STE-Labs/legacy-84/Chassis/Galaxy/230/2U/docs/bottom-gx283.png

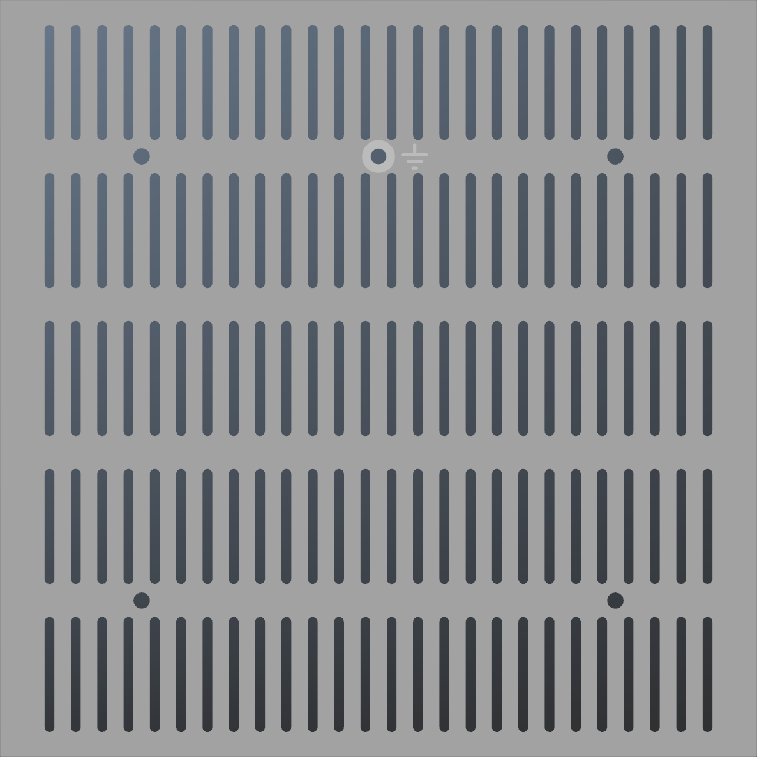
Chassis/Galaxy/230/2U/docs/bottom-gx283.png
