STE-Labs/legacy-84/Chassis/Galaxy/230/4U/docs/rear-xlr.png

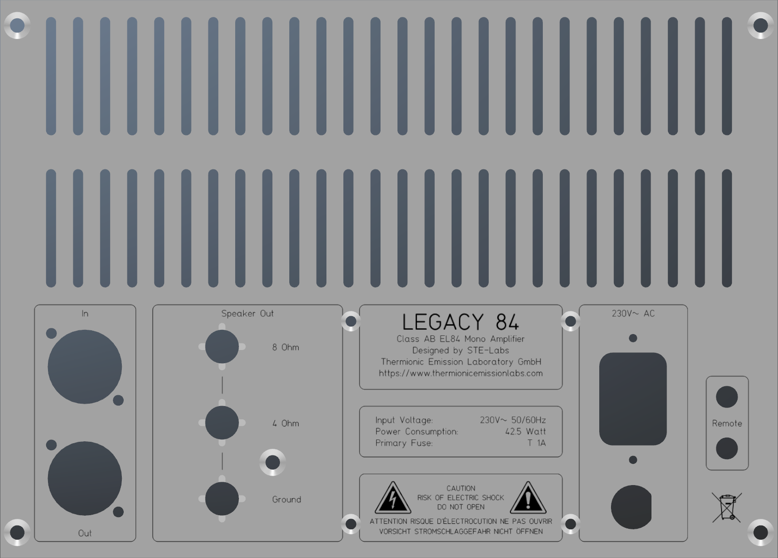
Chassis/Galaxy/230/4U/docs/rear-xlr.png
