STE-Labs/legacy-84/Chassis/Galaxy/330/2U/Renders/front-3-1.png

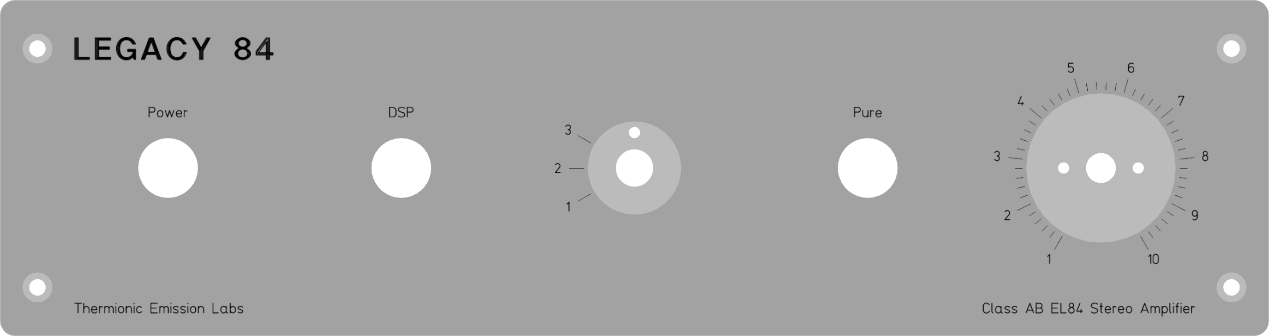
Chassis/Galaxy/330/2U/Renders/front-3-1.png
