STE-Labs/legacy-84/Chassis/Galaxy/330/2U/Renders/gx383-bottom.png

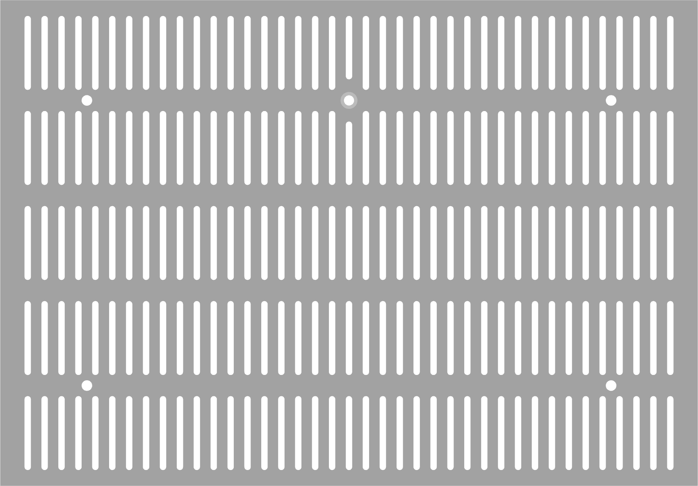
Chassis/Galaxy/330/2U/Renders/gx383-bottom.png
