STE-Labs/legacy-84/Chassis/Galaxy/330/2U/Renders/gx388-top.png

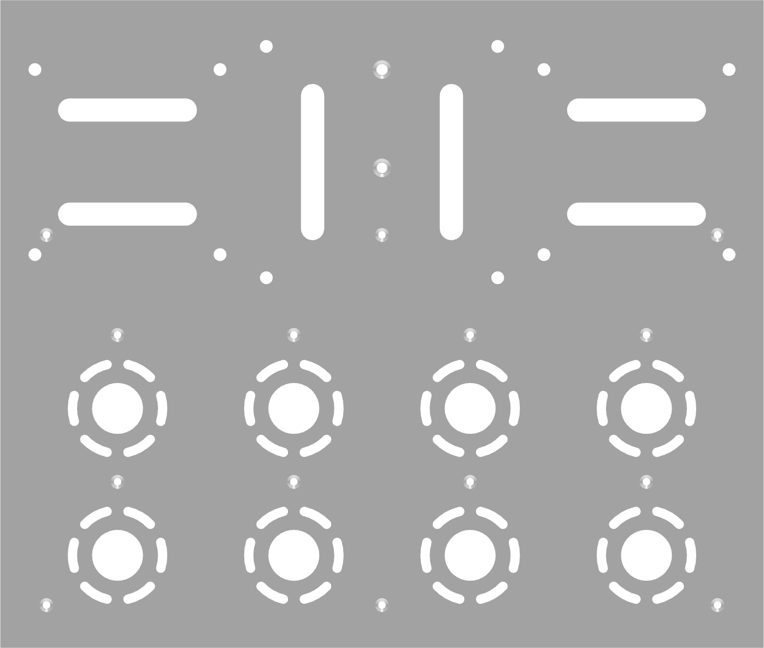
Chassis/Galaxy/330/2U/Renders/gx388-top.png
