STE-Labs/legacy-84/Chassis/Galaxy/330/2U/Renders/rear-3-1-xlr.png

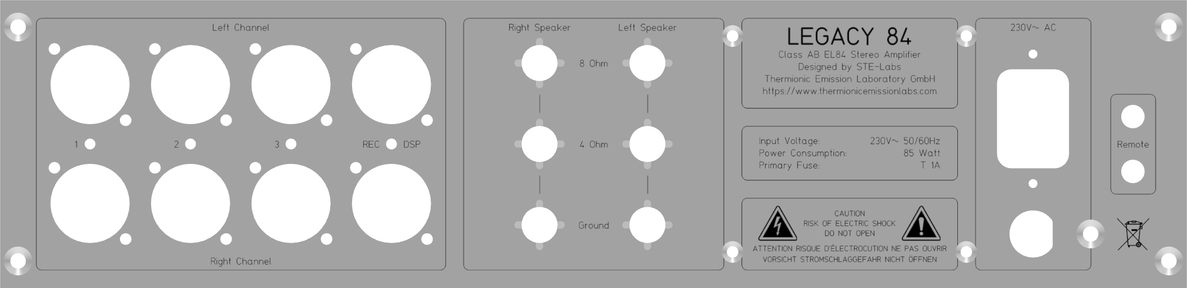
Chassis/Galaxy/330/2U/Renders/rear-3-1-xlr.png
