STE-Labs/legacy-84/Chassis/Galaxy/330/2U/Renders/rear-4-1-rca.png

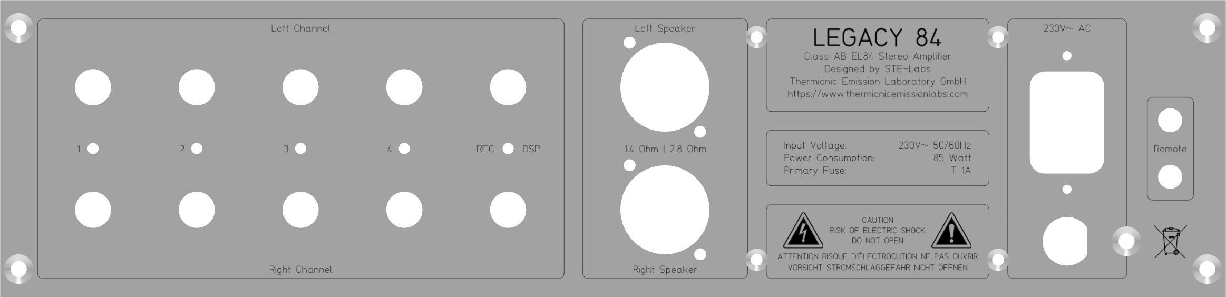
Chassis/Galaxy/330/2U/Renders/rear-4-1-rca.png
