STE-Labs/legacy-84/Chassis/Slimline/2U/docs/front.png

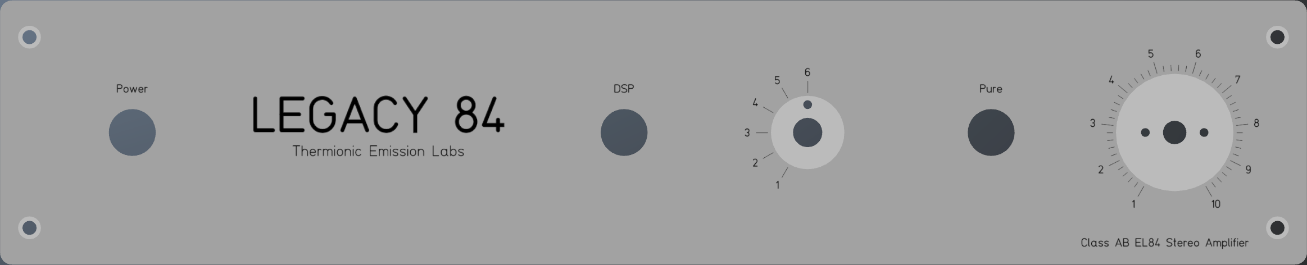
Chassis/Slimline/2U/docs/front.png
