STE-Labs/legacy-84/Chassis/Slimline/2U/docs/rear-xlr.png

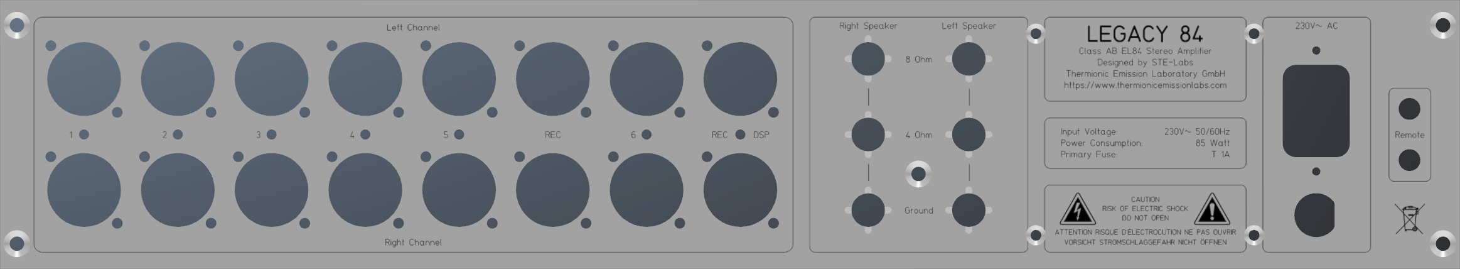
Chassis/Slimline/2U/docs/rear-xlr.png
