STE-Labs/legacy-84/transformers/AEE/open/1000014716.jpg

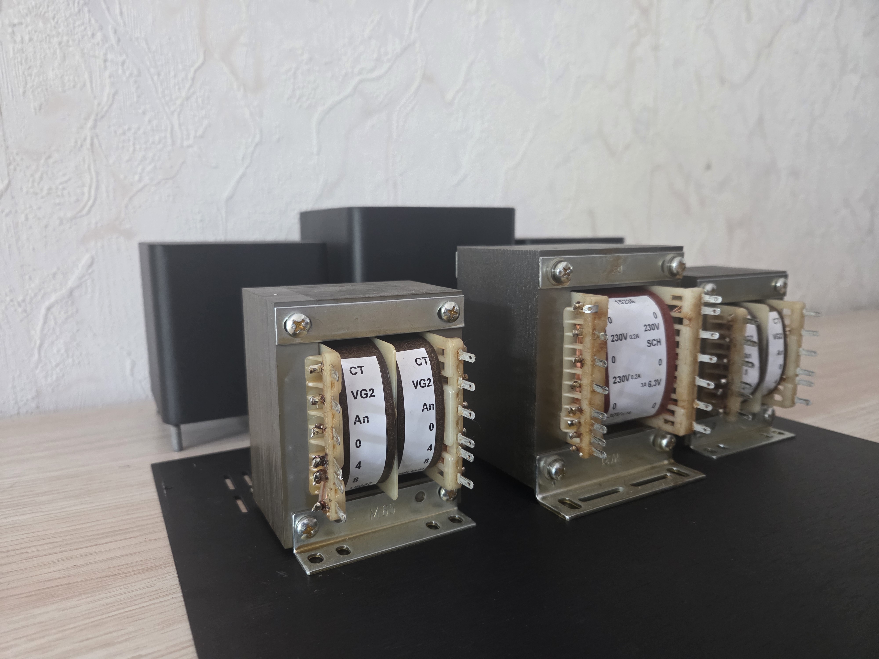
transformers/AEE/open/1000014716.jpg
