STE-Labs/legacy-84/transformers/AEE/open/1000014717.jpg

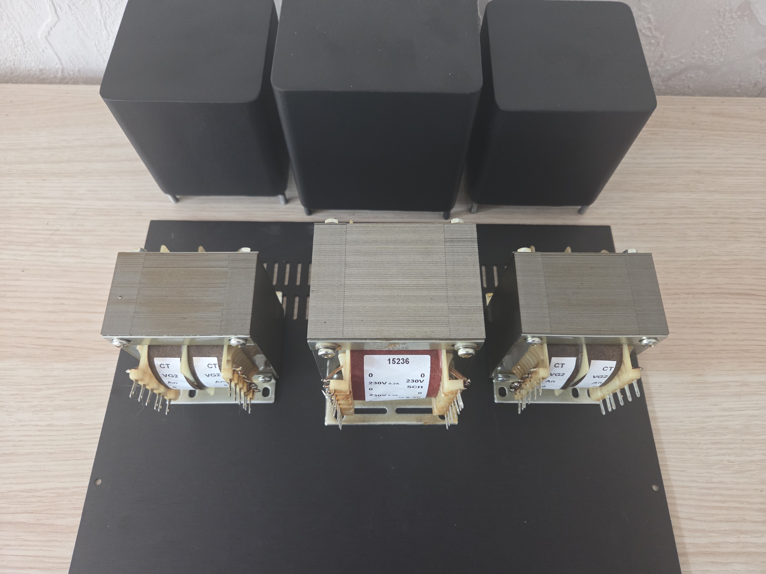
transformers/AEE/open/1000014717.jpg
