STE-Labs/legacy-84/transformers/AEE/open/1000014719.jpg

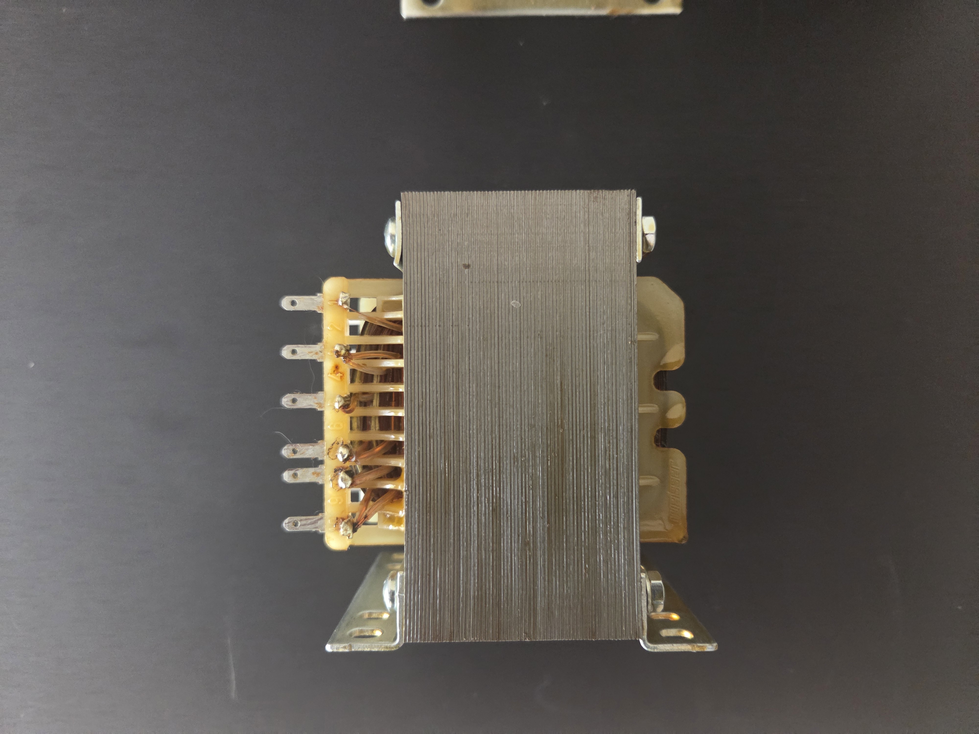
transformers/AEE/open/1000014719.jpg
