STE-Labs/legacy-84/transformers/AEE/open/1000014720.jpg

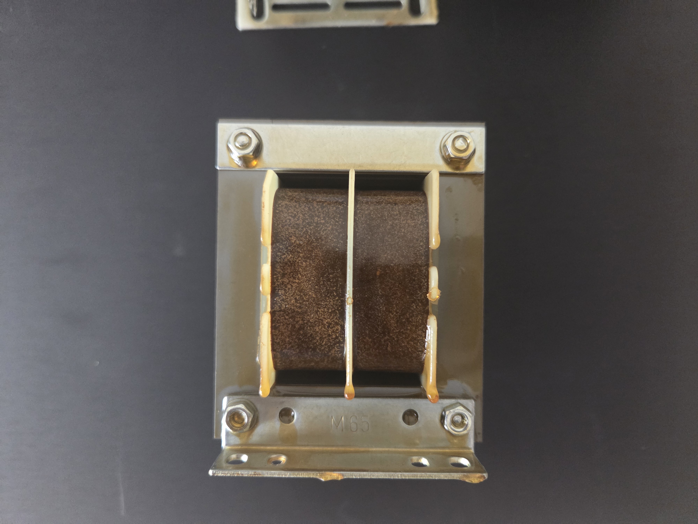
transformers/AEE/open/1000014720.jpg
