STE-Labs/legacy-84/transformers/AEE/open/1000014721.jpg

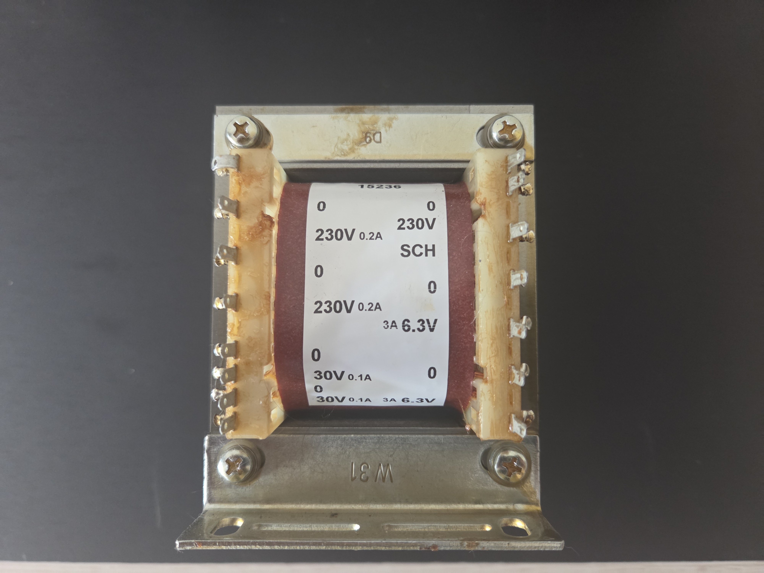
transformers/AEE/open/1000014721.jpg
