STE-Labs/legacy-84/transformers/AEE/potted/1000014724.jpg

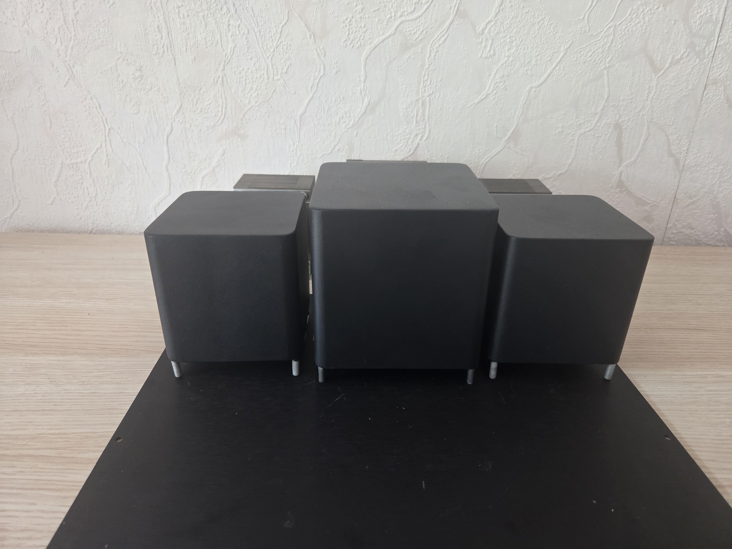
transformers/AEE/potted/1000014724.jpg
