STE-Labs/legacy-84/transformers/AEE/potted/1000014725.jpg

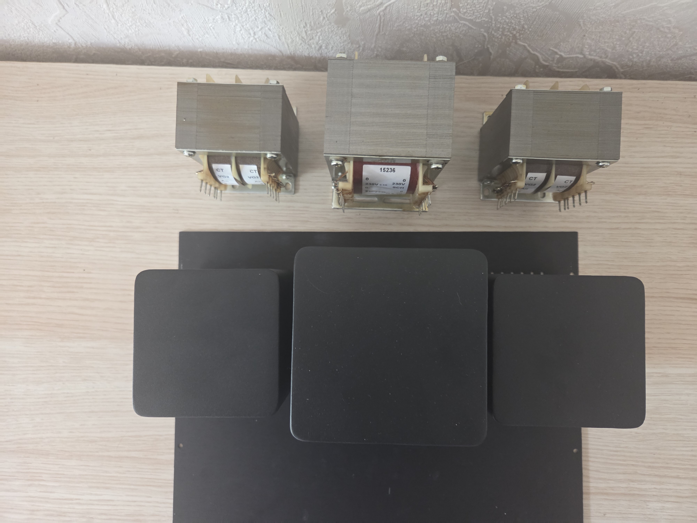
transformers/AEE/potted/1000014725.jpg
