STE-Labs/legacy-84/transformers/AEE/potted/1000014728.jpg

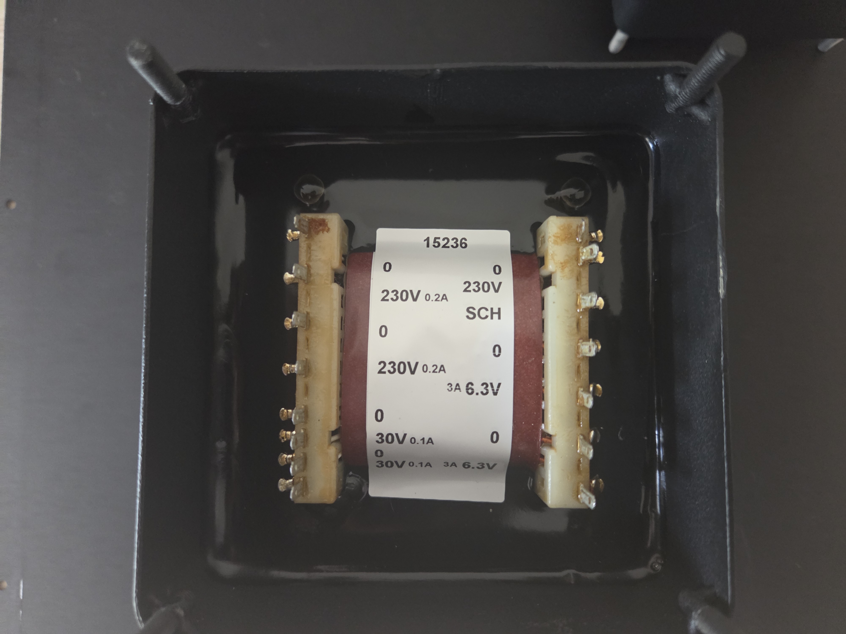
transformers/AEE/potted/1000014728.jpg
