STE-Labs/legacy-84/transformers/AEE/potted/1000014729.jpg

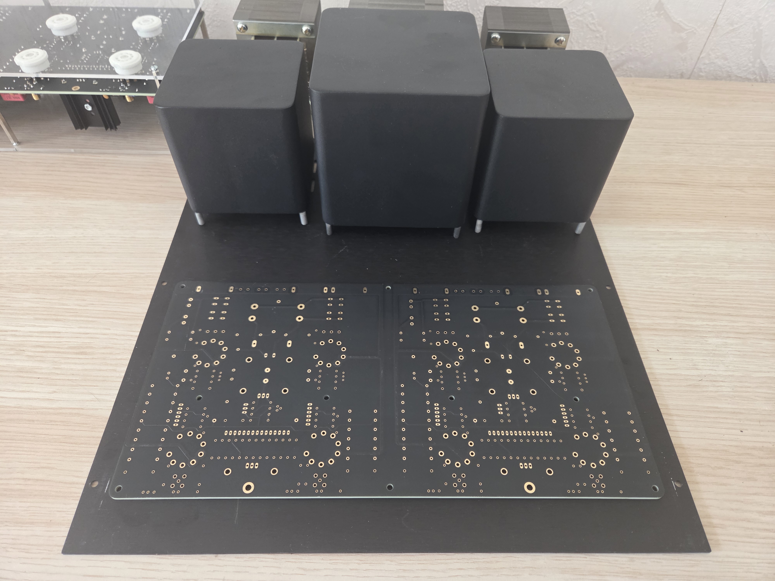
transformers/AEE/potted/1000014729.jpg
