STE-Labs/legacy-84/legacy-84-mono-inverted/docs/circuit-diagram-pure-switch.pdf

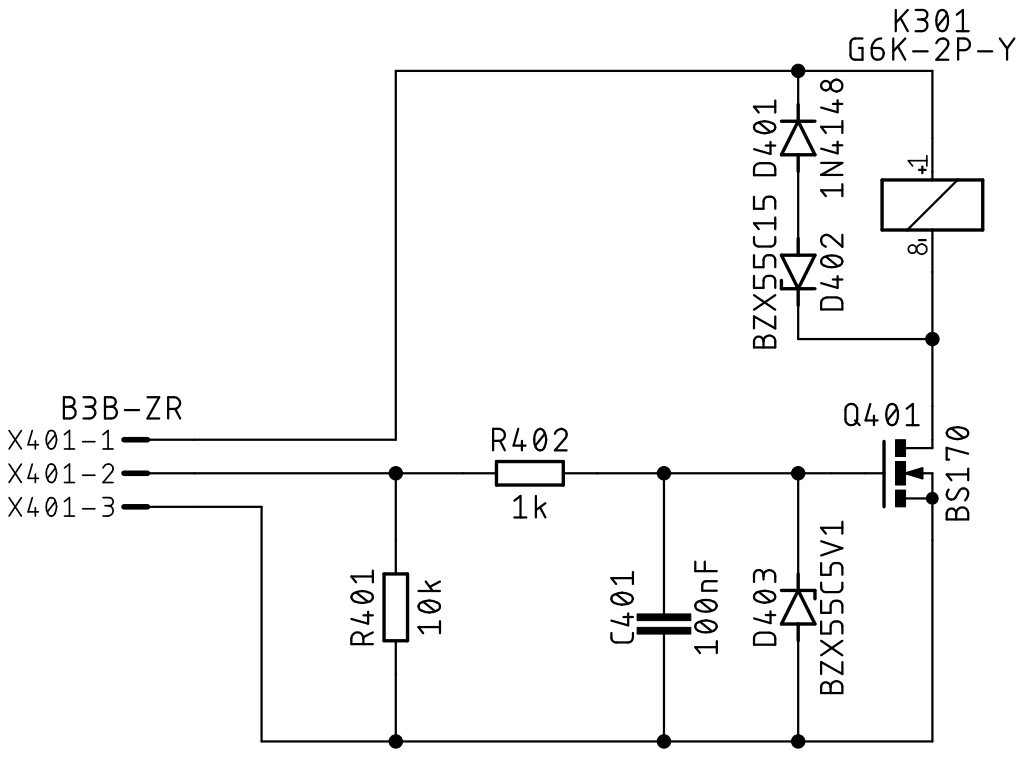
[picture p122: page 1]
