STE-Labs/legacy-84/legacy-84-mono/docs/circuit-diagram-amplifier.pdf

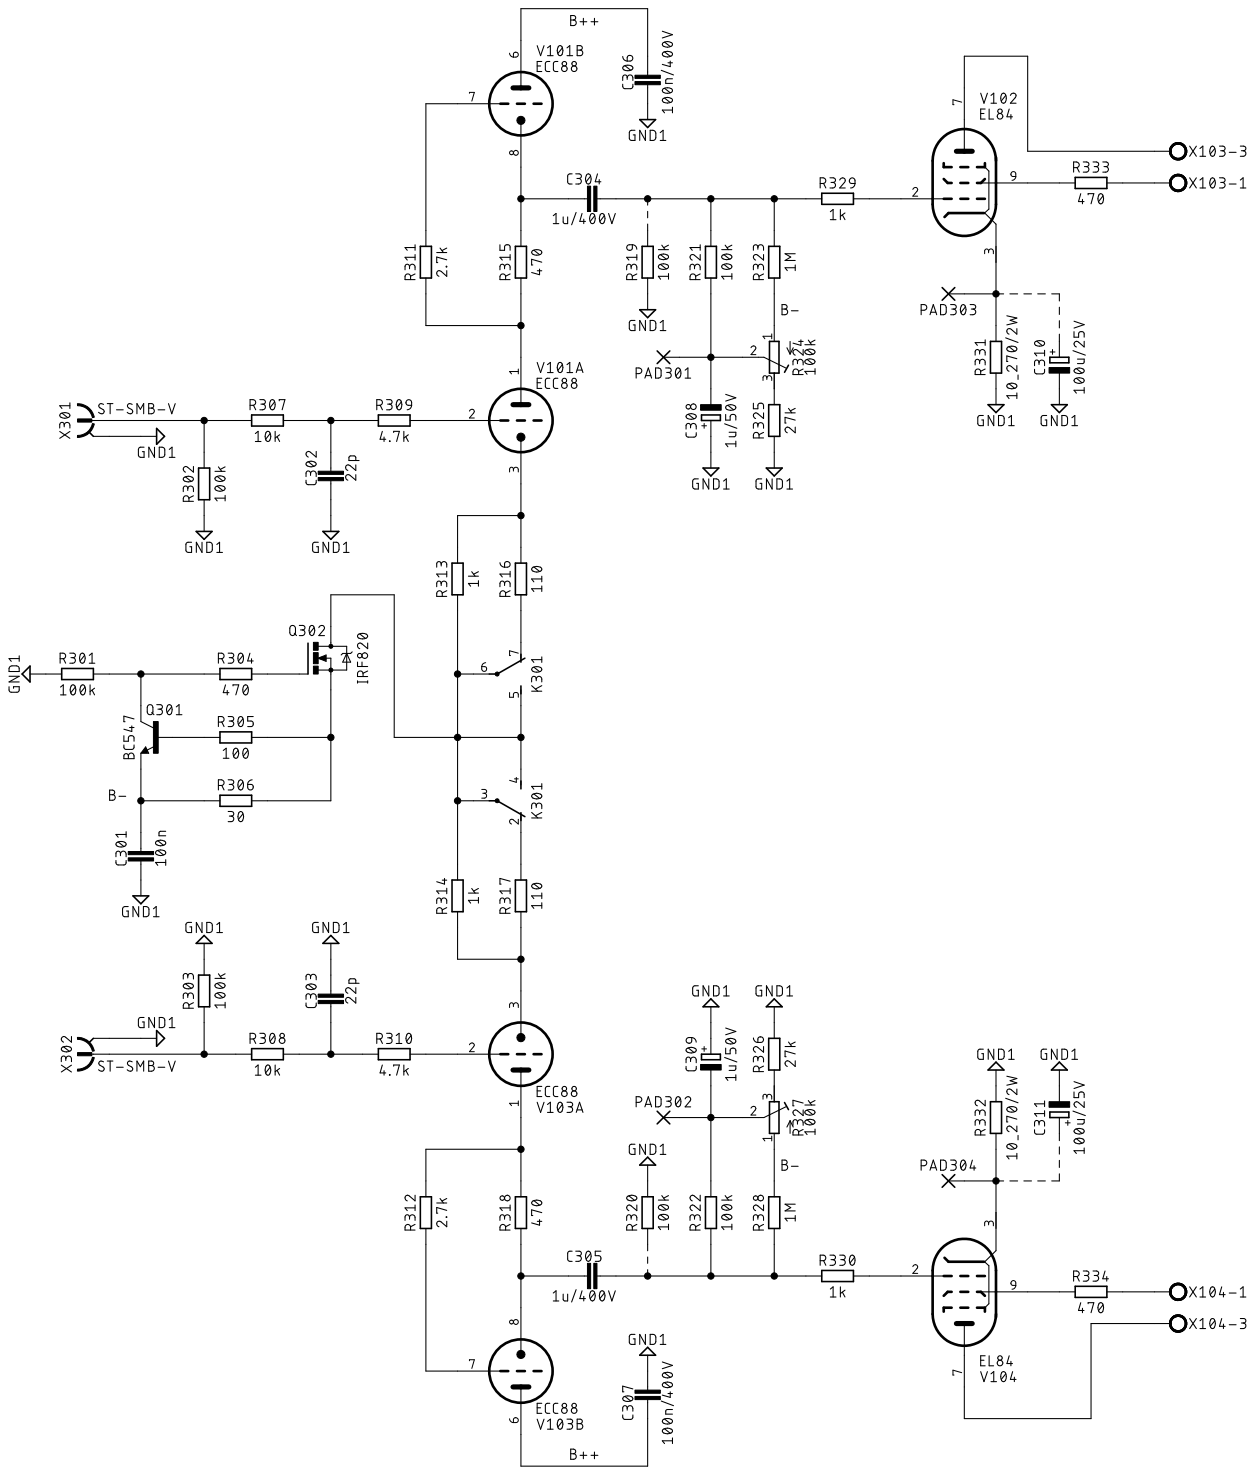
[picture p123: page 1]
