STE-Labs/legacy-84/legacy-84-mono/docs/circuit-diagram-negative-power-supply.pdf

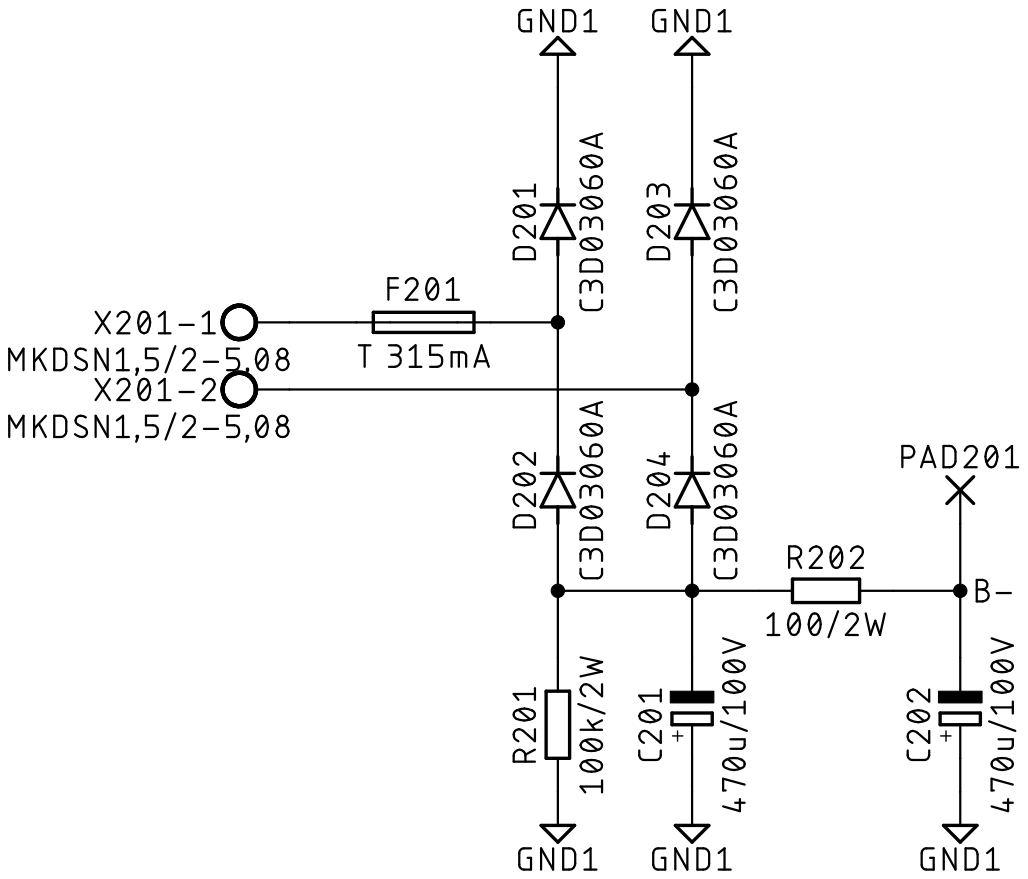
[picture p124: page 1]
