STE-Labs/legacy-84/legacy-84-mono/docs/circuit-diagram-power-supply.pdf

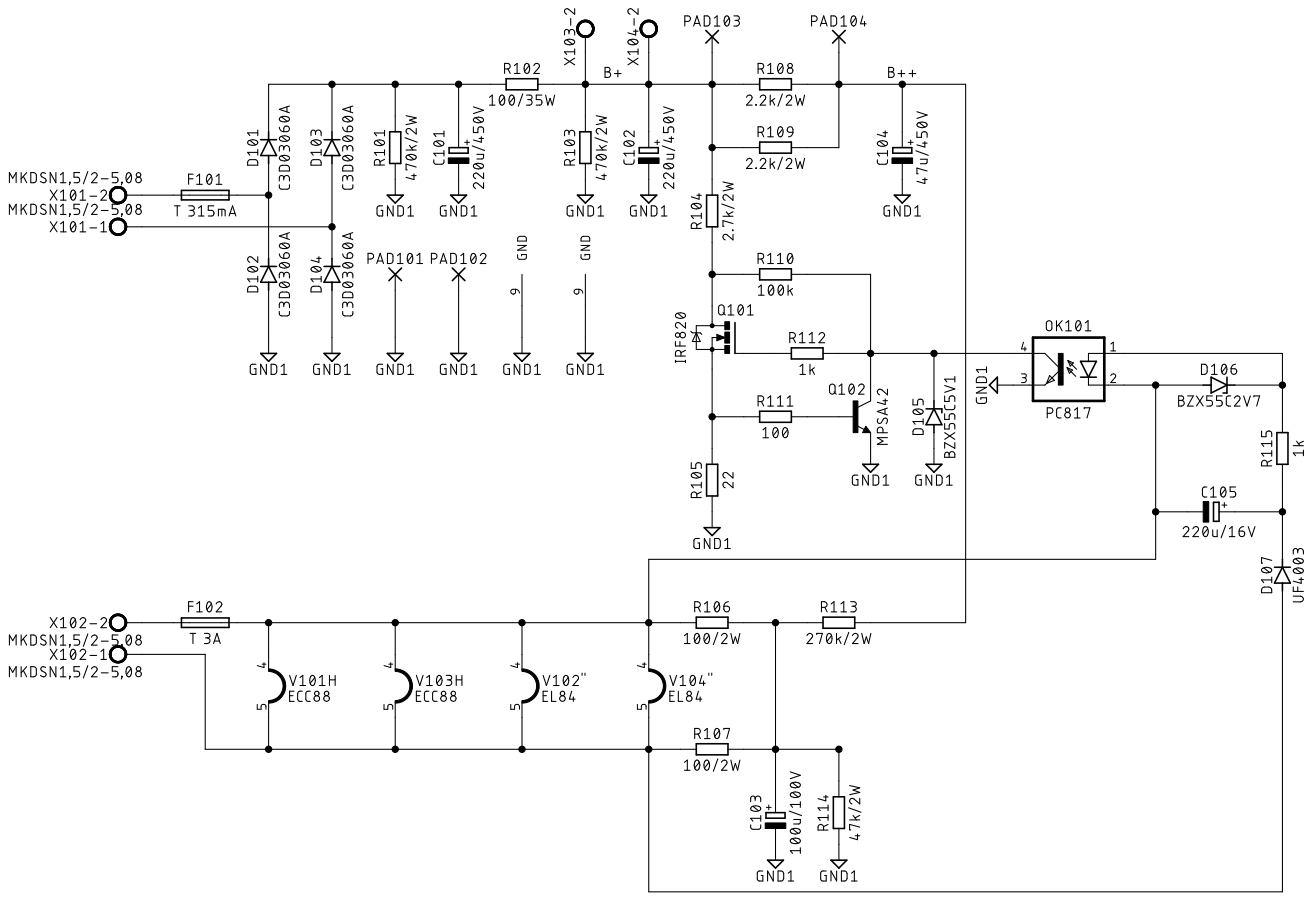
[picture p125: page 1]
