STE-Labs/legacy-84/legacy-84-mono/docs/circuit-diagram-pure-switch.pdf

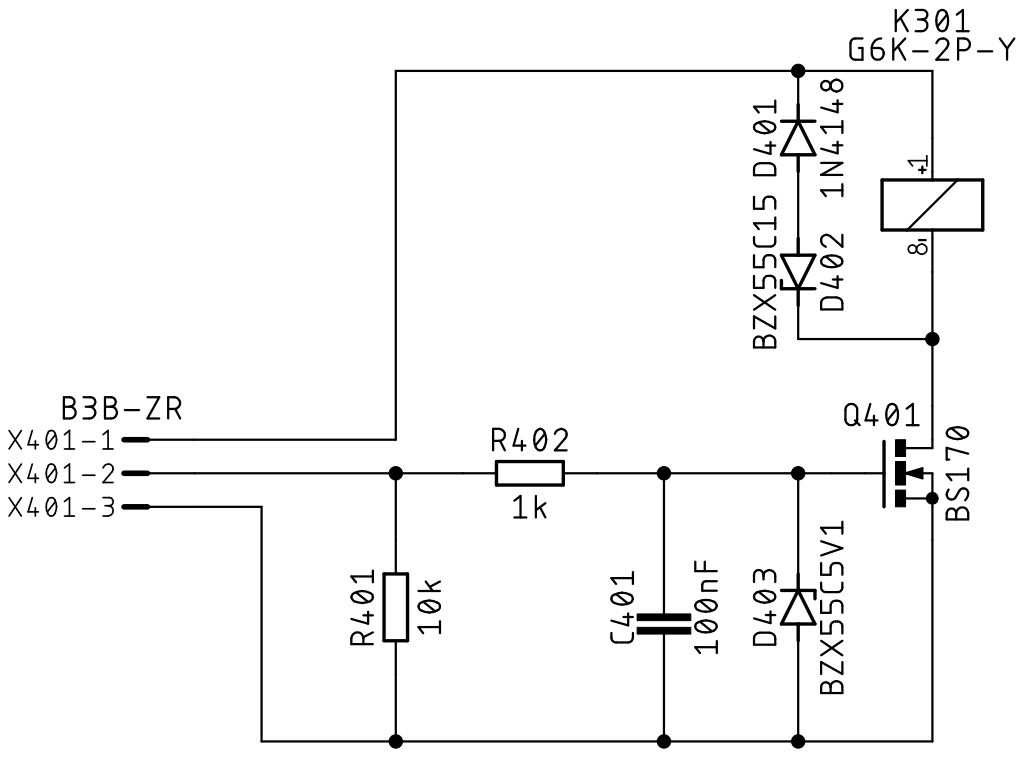
[picture p126: page 1]
