STE-Labs/legacy-84/legacy-84-stereo/docs/circuit-diagram-left-channel-negative-power-supply.pdf

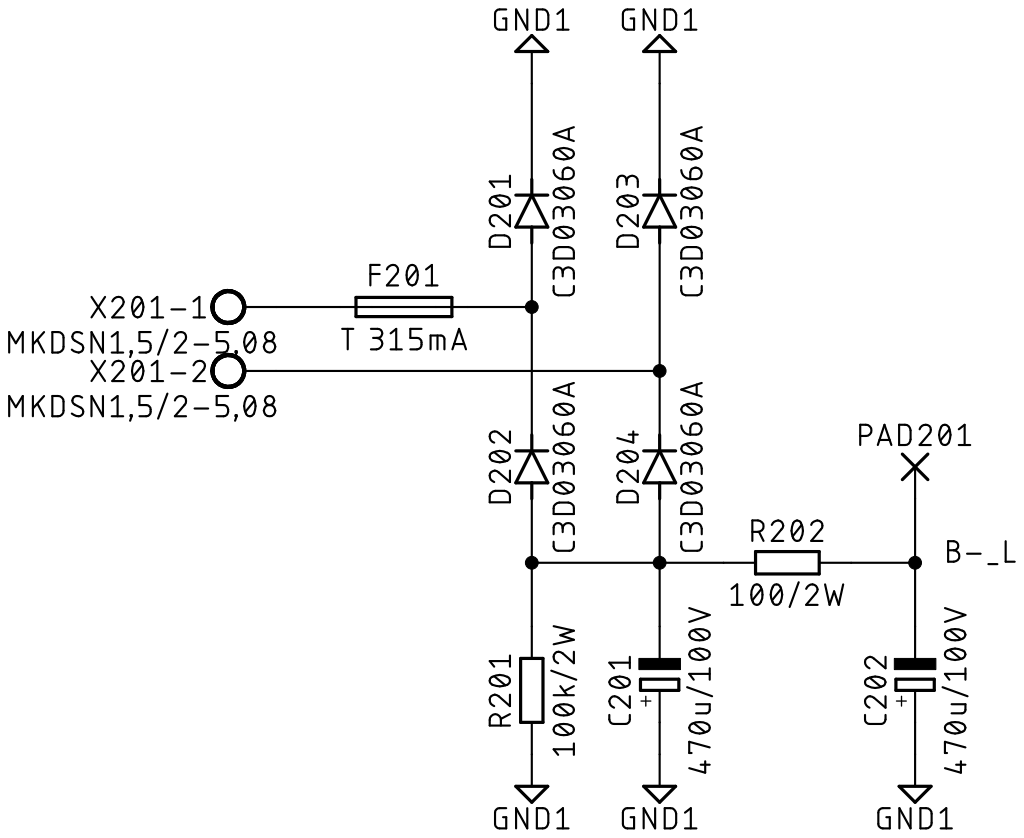
[picture p127: page 1]
