STE-Labs/legacy-84/legacy-84-stereo/docs/circuit-diagram-left-channel.pdf

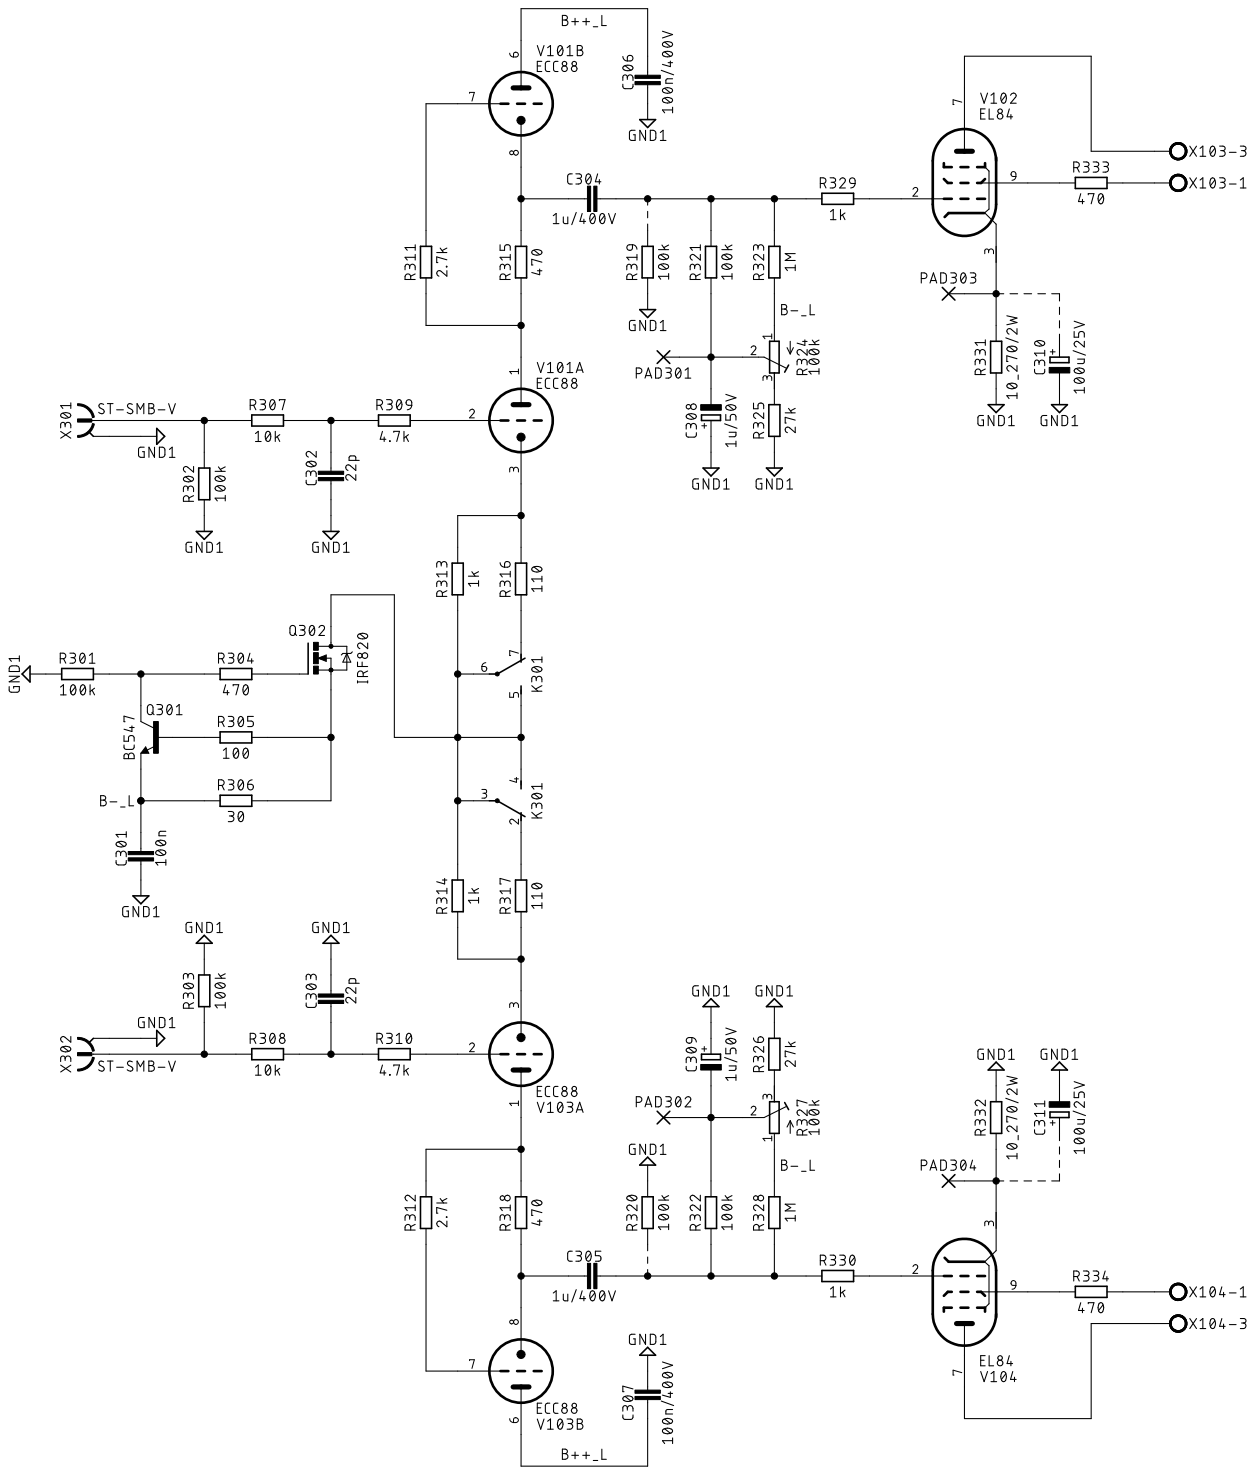
[picture p128: page 1]
