STE-Labs/legacy-84/legacy-84-stereo/docs/circuit-diagram-pure-switch.pdf

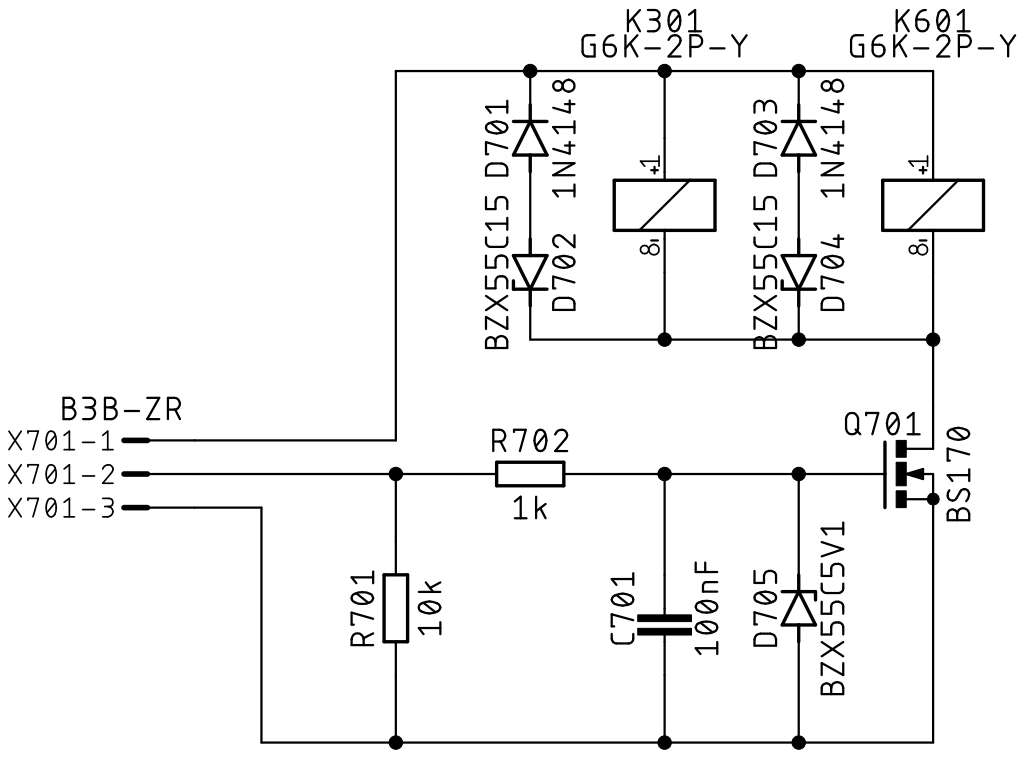
[picture p129: page 1]
