STE-Labs/legacy-84/legacy-84-stereo/docs/circuit-diagram-right-channel-negative-power-supply.pdf

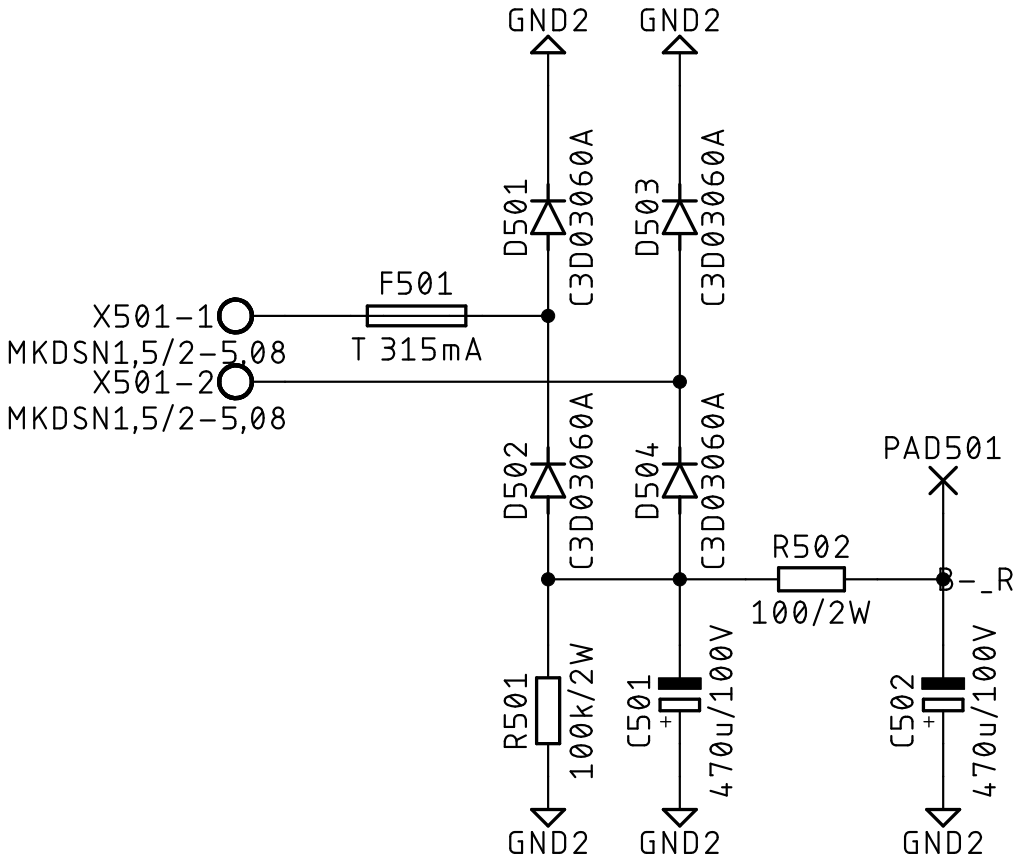
[picture p130: page 1]
