STE-Labs/legacy-84/legacy-84-stereo/docs/circuit-diagram-right-channel.pdf

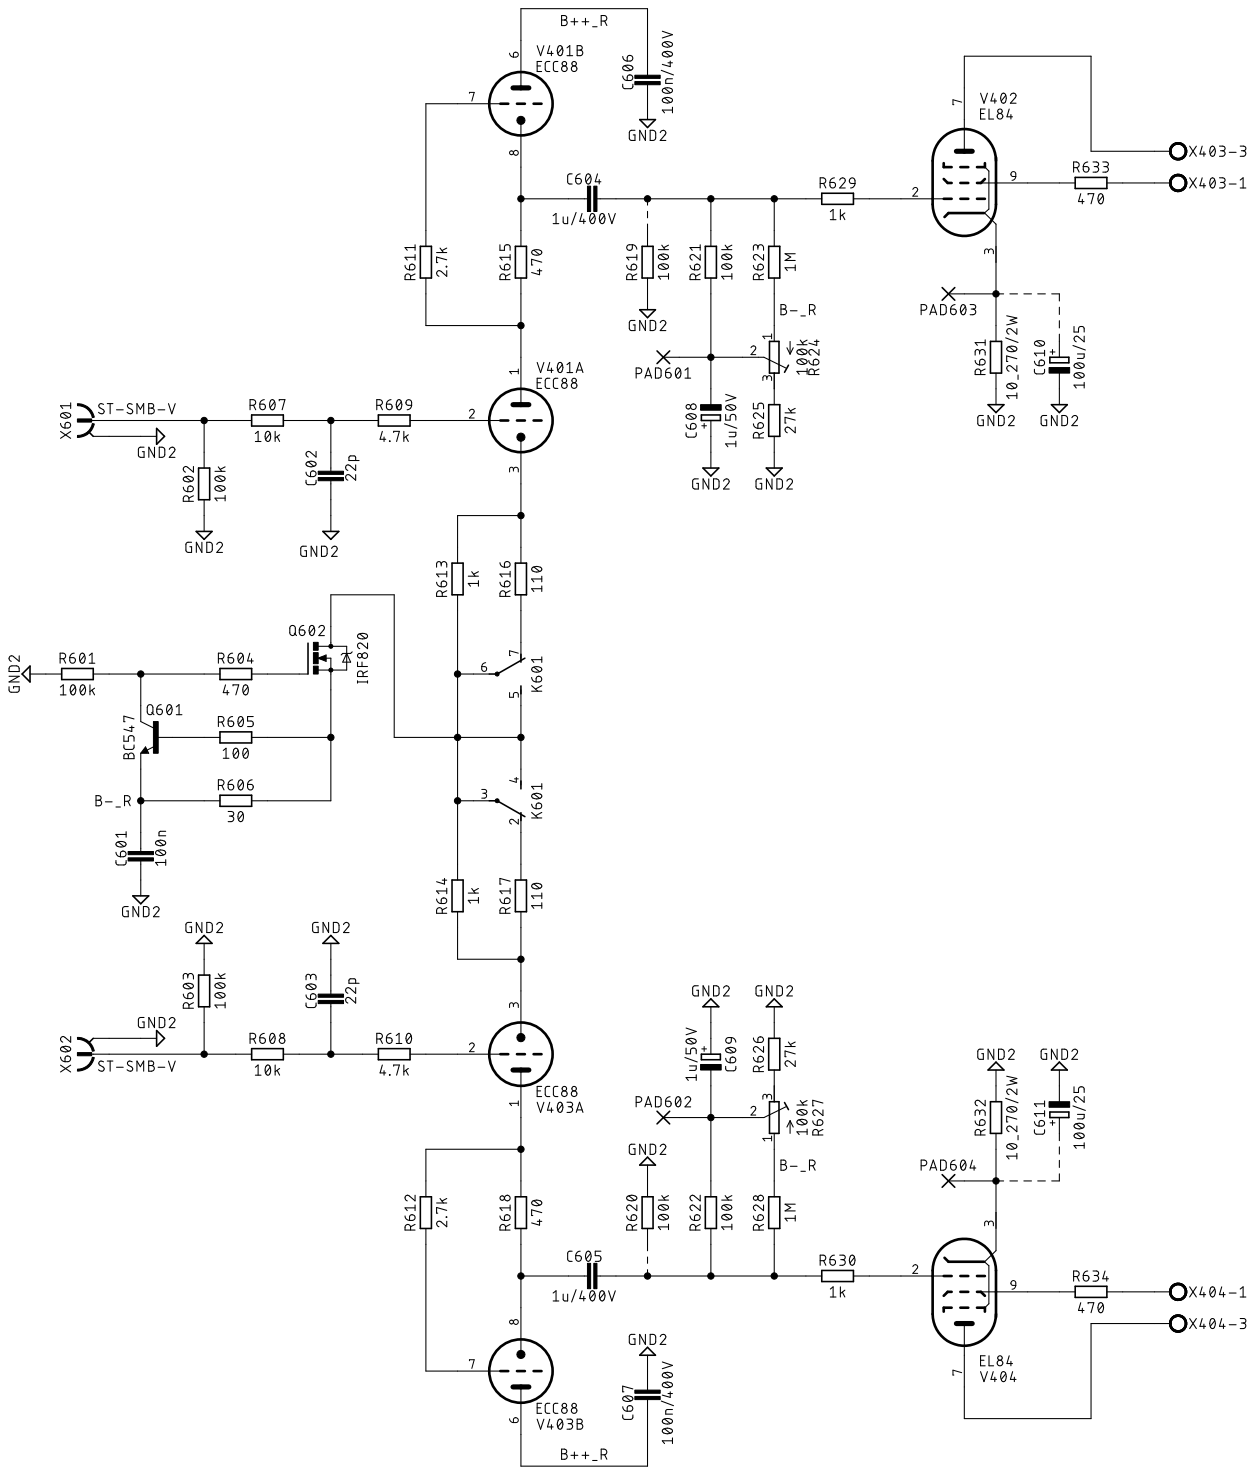
[picture p131: page 1]
